ak66666/ThumbsUp-Trackball-v5-Omron/Dongle Case/Cura Positioning.png

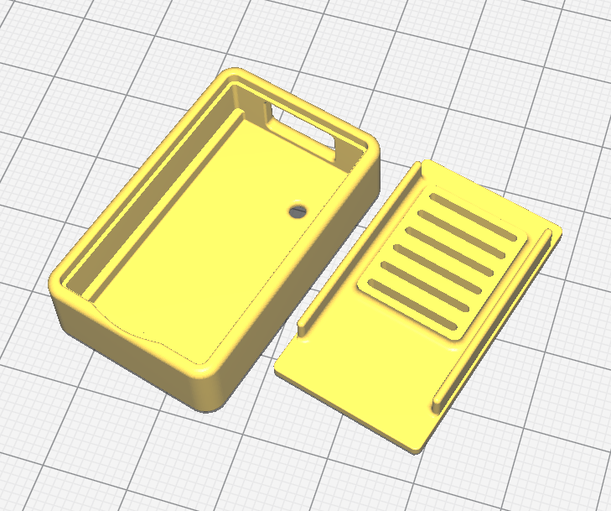
Dongle Case/Cura Positioning.png
