ak66666/ThumbsUp-Trackball-v5-Omron/Dongle Case/Model.png

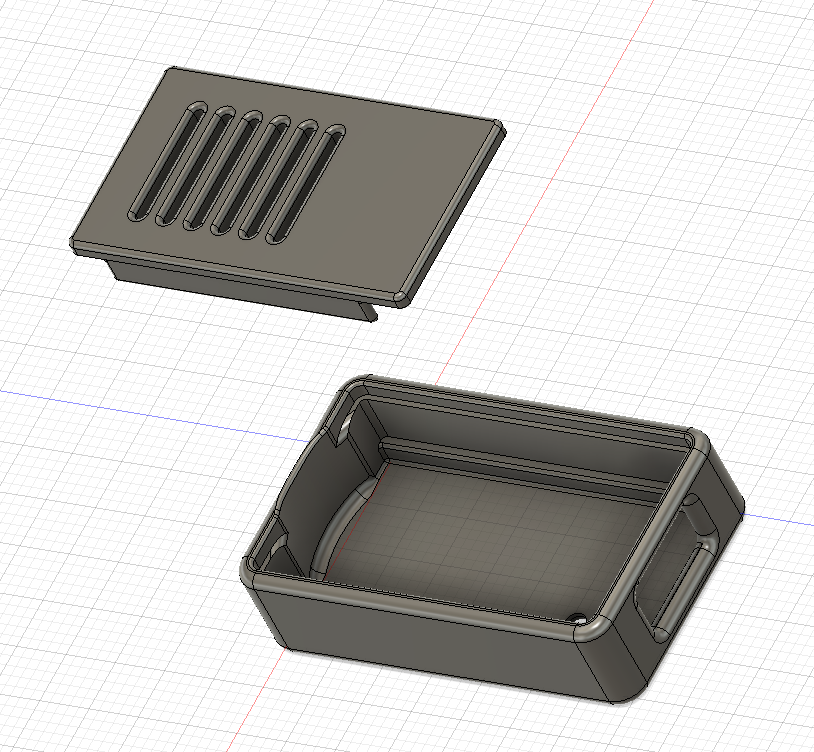
Dongle Case/Model.png
