ak66666/ThumbsUp-Trackball-v5-Omron/Kicad/Trackball/Pictures/PCBs.jpg

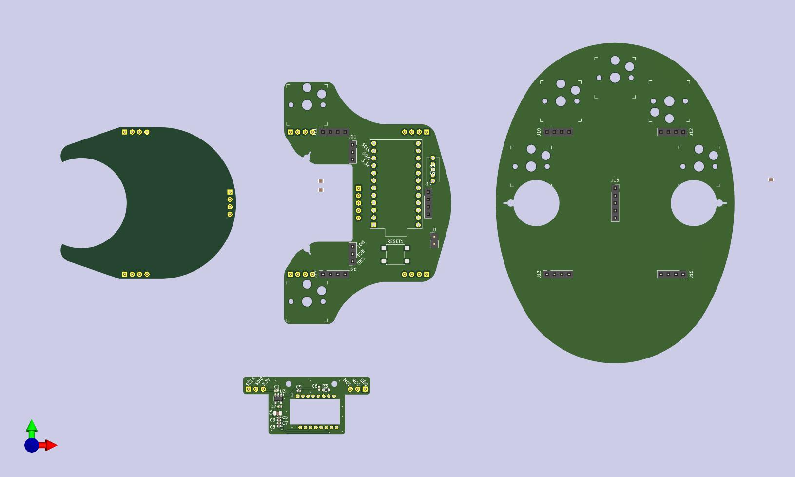
Kicad/Trackball/Pictures/PCBs.jpg
