ak66666/ThumbsUp-Trackball-v5-Omron/Photos/rev1 PCB Totem Pole, Back.png

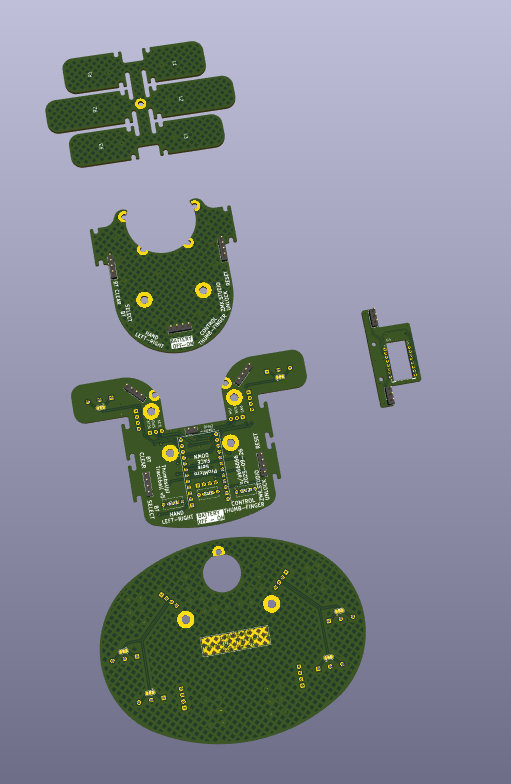
Photos/rev1 PCB Totem Pole, Back.png
