ak66666/ThumbsUp-Trackball-v5-Omron/Photos/v4rev1/IMG_20251021_160033889.jpg

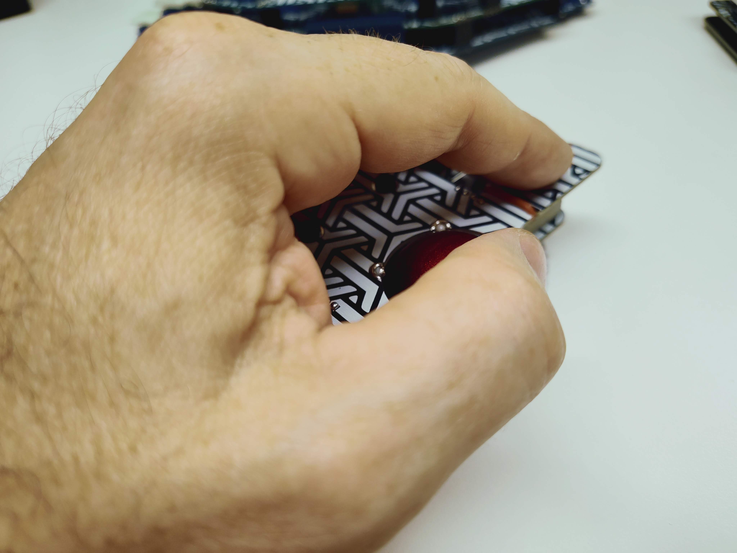
Photos/v4rev1/IMG_20251021_160033889.jpg
