ak66666/ThumbsUp-Trackball-v5-Omron/3D Parts/Cover Left Hand, Back View.png

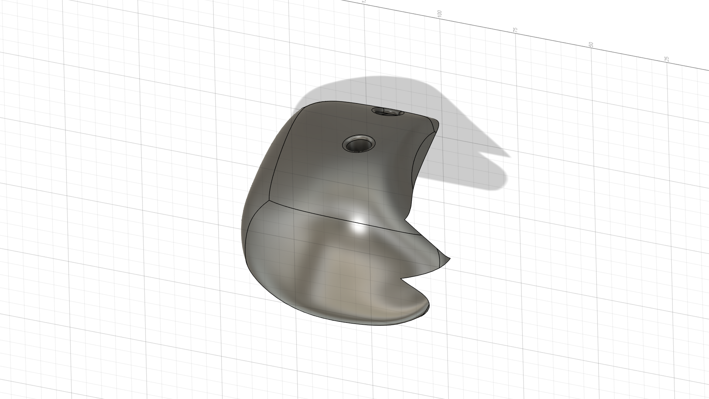
3D Parts/Cover Left Hand, Back View.png
