ak66666/ThumbsUp-Trackball-v5-Omron/3D Parts/Flap Holder.stl

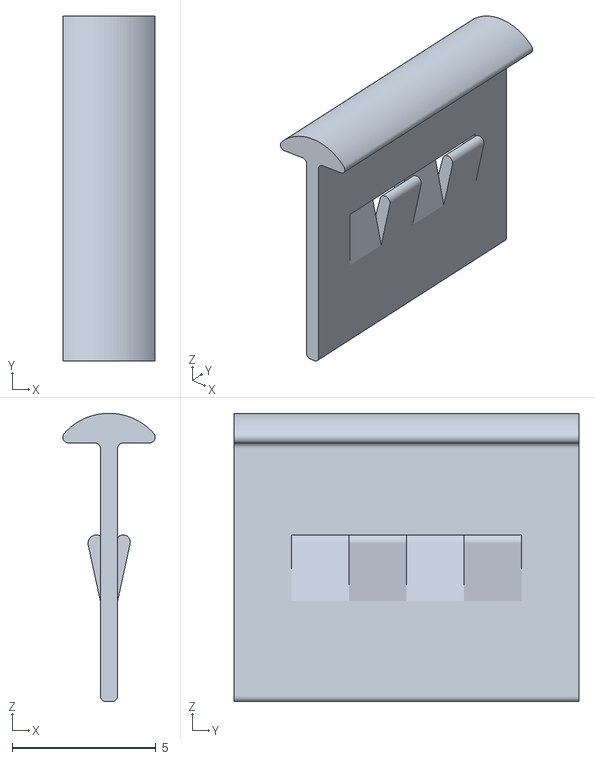
[picture p56: CAD file, 2025-10-11]
3D Parts/Flap Holder.stl
3.21 x 12.0 x 10.0
