ak66666/ThumbsUp-Trackball-v5-Omron/Kicad/Trackball/1825232-1/3D/1825232-1.stp

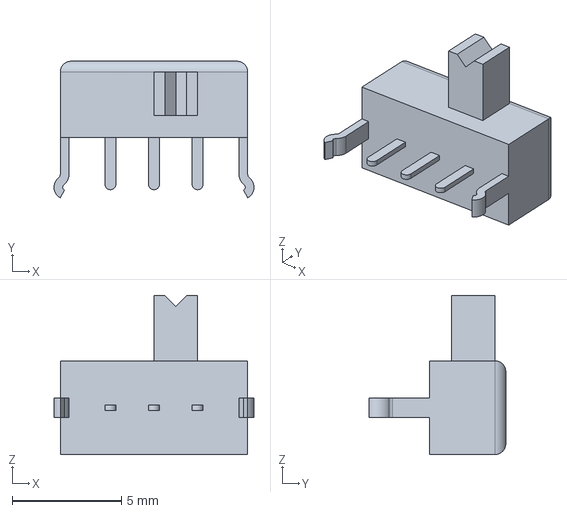
[picture p57: CAD file, 2025-09-26]
Kicad/Trackball/1825232-1/3D/1825232-1.stp
9.17 x 6.27 x 7.30 mm
