ak66666/ThumbsUp-Trackball-v5-Omron/Photos/Assembly Process/IMG_20250912_110447390.jpg

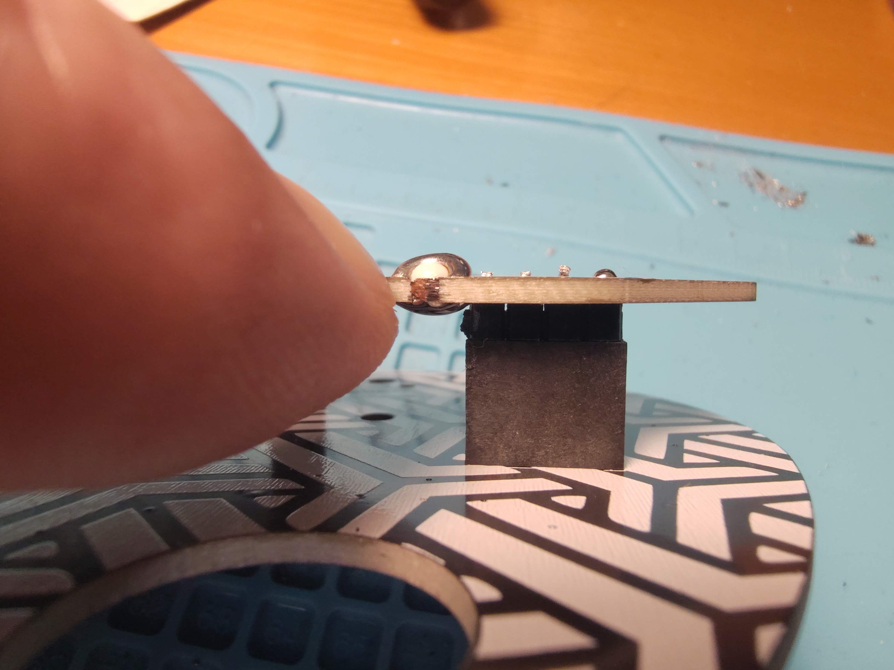
Photos/Assembly Process/IMG_20250912_110447390.jpg
