ak66666/ThumbsUp-Trackball-v5-Omron/Photos/Assembly Process/IMG_20250912_112219243_HDR.jpg

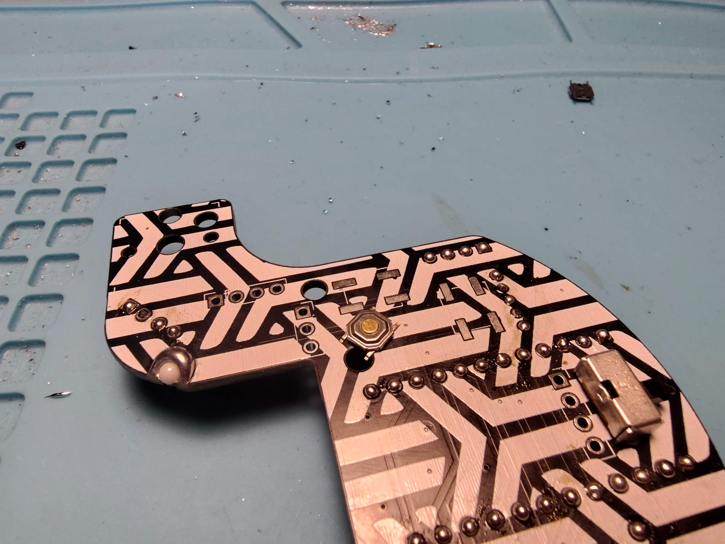
Photos/Assembly Process/IMG_20250912_112219243_HDR.jpg
