ak66666/ThumbsUp-Trackball-v5-Omron/Photos/Assembly Process/IMG_20250912_112803096_HDR.jpg

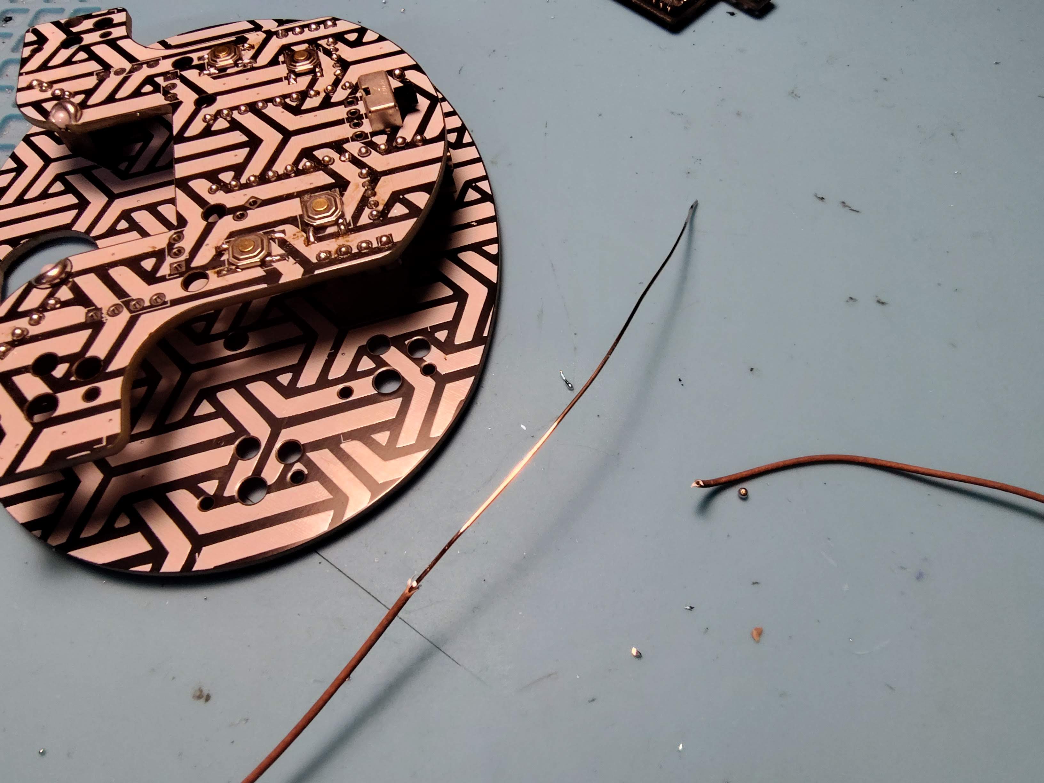
Photos/Assembly Process/IMG_20250912_112803096_HDR.jpg
