ak66666/ThumbsUp-Trackball-v5-Omron/Photos/Assembly Process/IMG_20250912_113752580_HDR.jpg

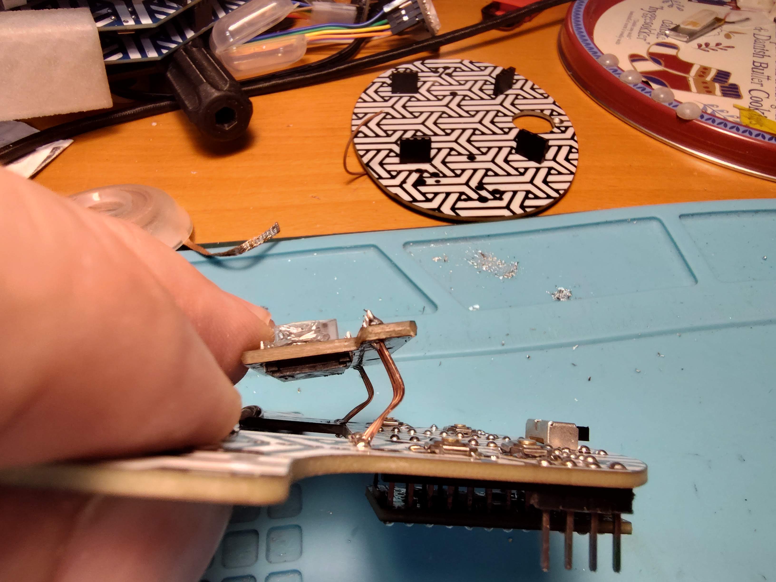
Photos/Assembly Process/IMG_20250912_113752580_HDR.jpg
