ak66666/ThumbsUp-Trackball-v5-Omron/Photos/Assembly Process/IMG_20250912_113833317.jpg

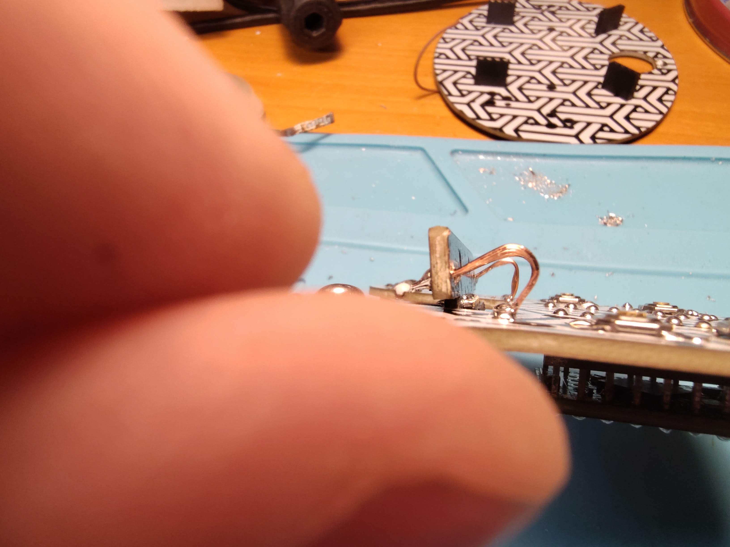
Photos/Assembly Process/IMG_20250912_113833317.jpg
